zane797/Pinewood-Derby-Timer/Photos/Exterior/20250219_124307.jpg

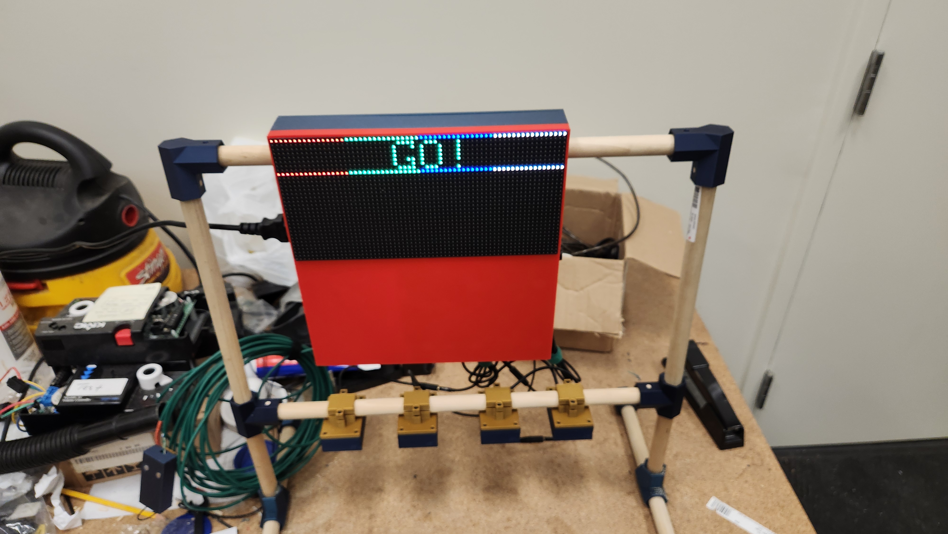
Photos/Exterior/20250219_124307.jpg
