zane797/Pinewood-Derby-Timer/Photos/Interior/20250219_135802.jpg

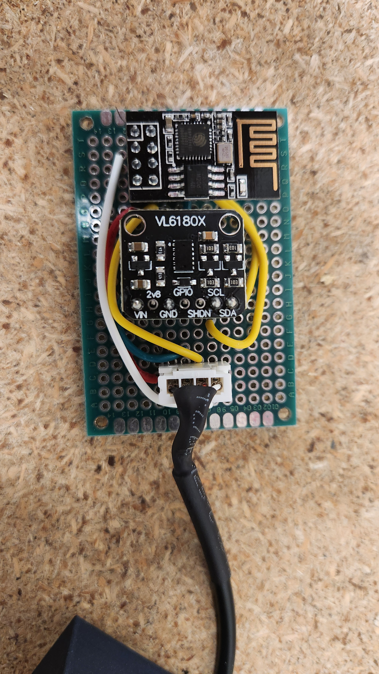
Photos/Interior/20250219_135802.jpg
