zane797/Pinewood-Derby-Timer/Photos/Interior/20250219_140125.jpg

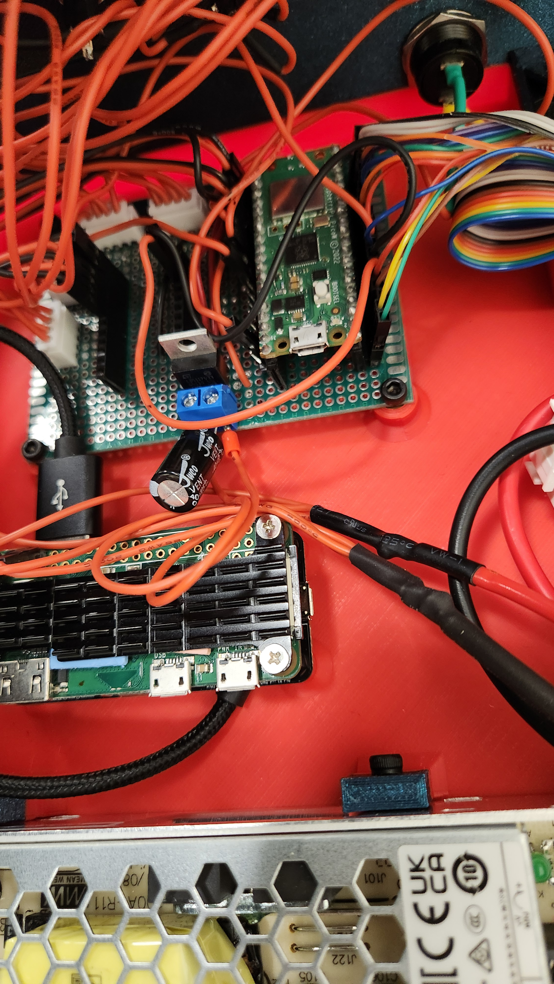
Photos/Interior/20250219_140125.jpg
