zane797/Pinewood-Derby-Timer/Photos/Interior/20250219_135758.jpg

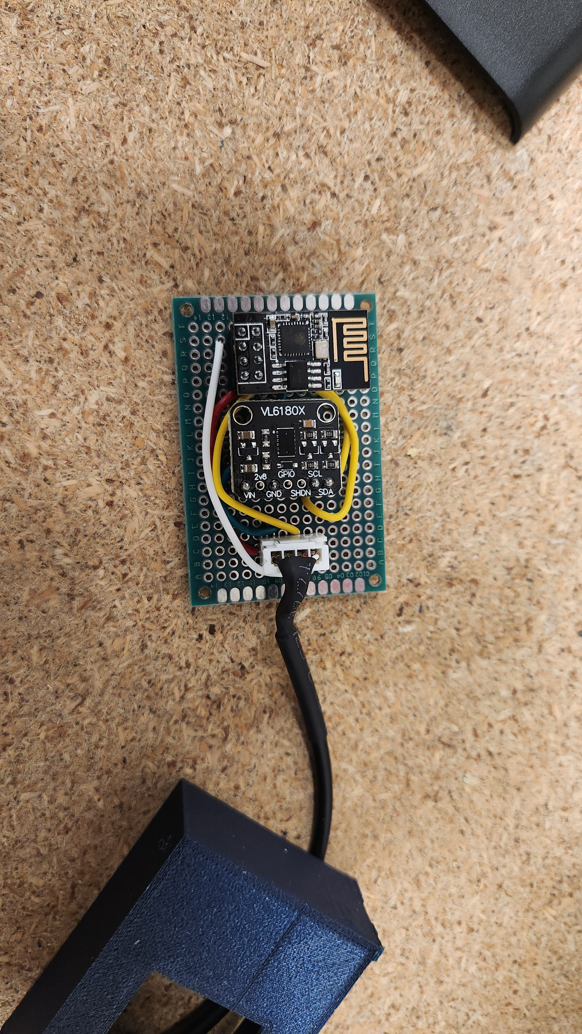
Photos/Interior/20250219_135758.jpg
