zane797/Pinewood-Derby-Timer/Photos/Interior/20250219_140120.jpg

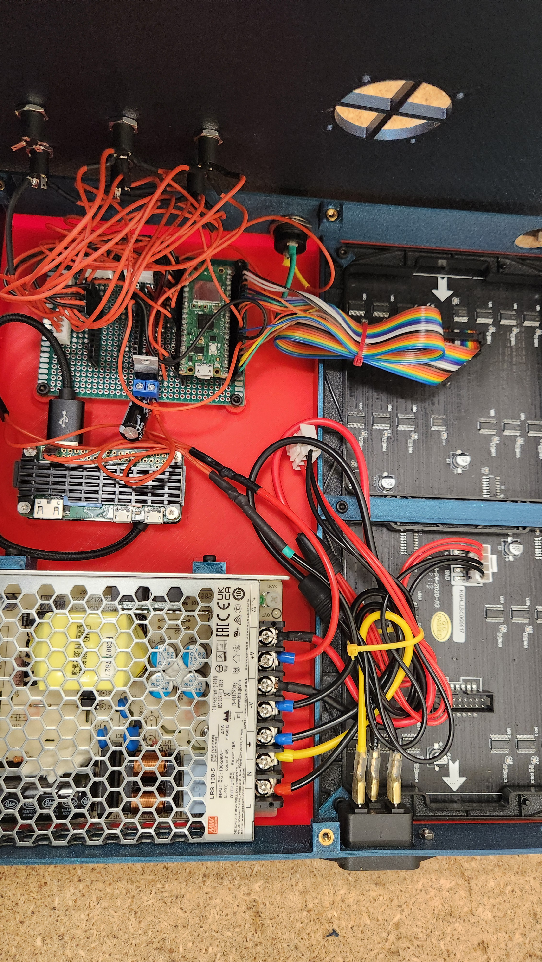
Photos/Interior/20250219_140120.jpg
